OLIMEX/Neo6502pc/DOCUMENTS/Neo6502pc-1.jpg

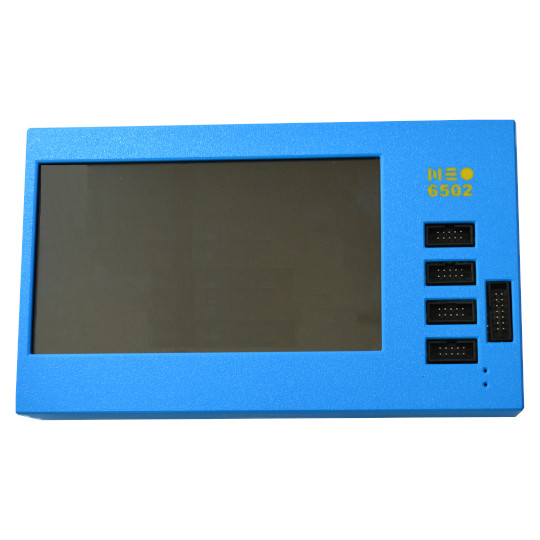
DOCUMENTS/Neo6502pc-1.jpg
