OLIMEX/Neo6502pc/DOCUMENTS/Neo6502pc-3.jpg

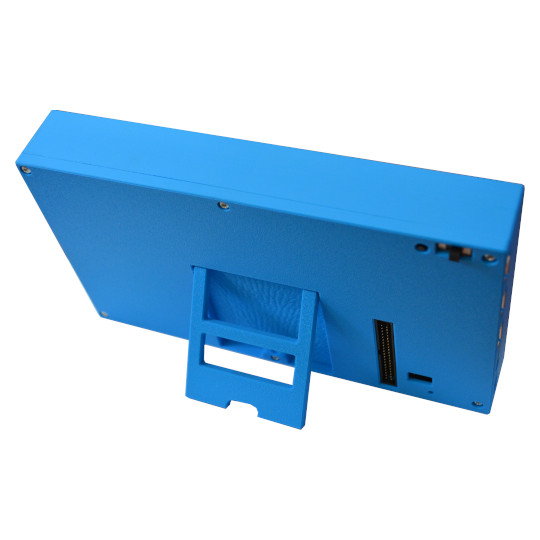
DOCUMENTS/Neo6502pc-3.jpg
