OLIMEX/Neo6502pc/DOCUMENTS/Neo6502pc-4.jpg

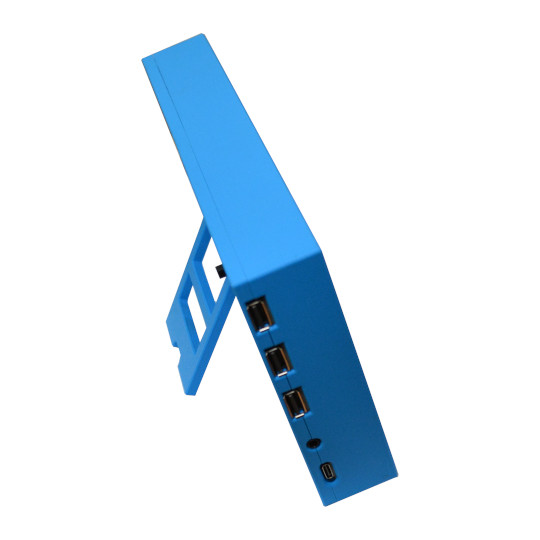
DOCUMENTS/Neo6502pc-4.jpg
