OLIMEX/Neo6502pc/DOCUMENTS/Neo6502pc-8.jpg

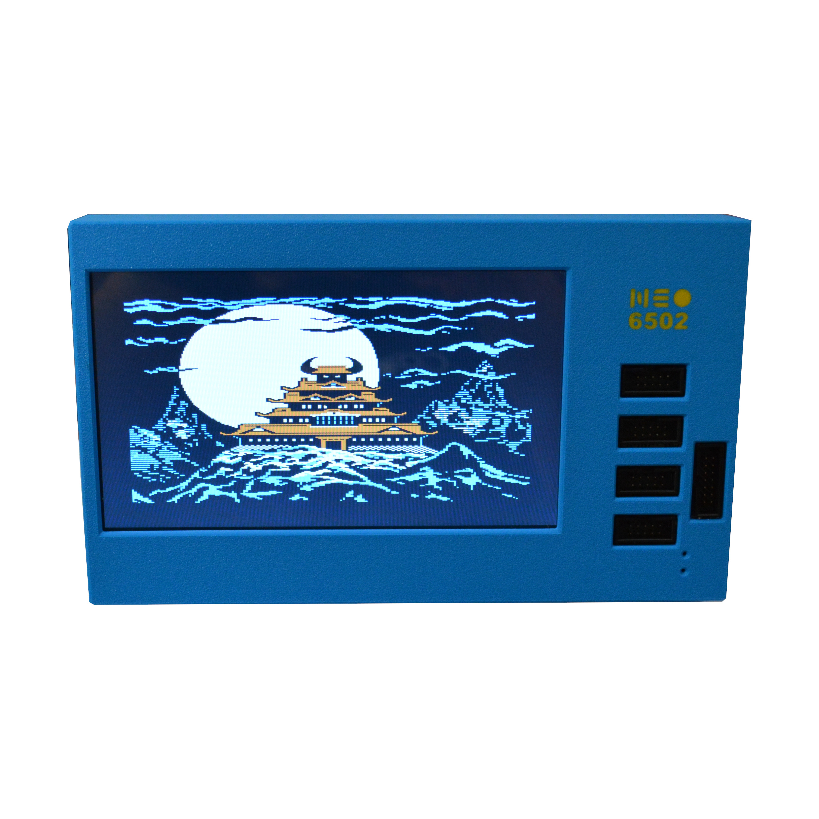
DOCUMENTS/Neo6502pc-8.jpg
